r0b0t1cu/Tastatura-Cobra/IMG/IMG_9379.jpg

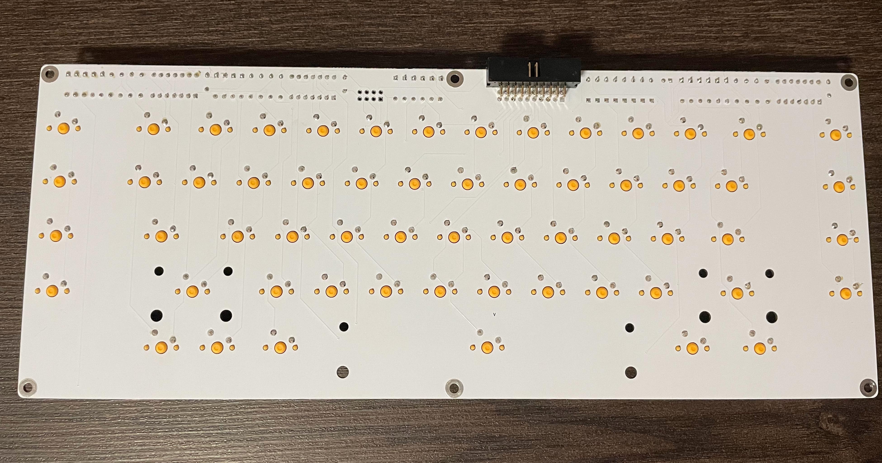
IMG/IMG_9379.jpg
