r0b0t1cu/Tastatura-Cobra/IMG/IMG_9391.jpg

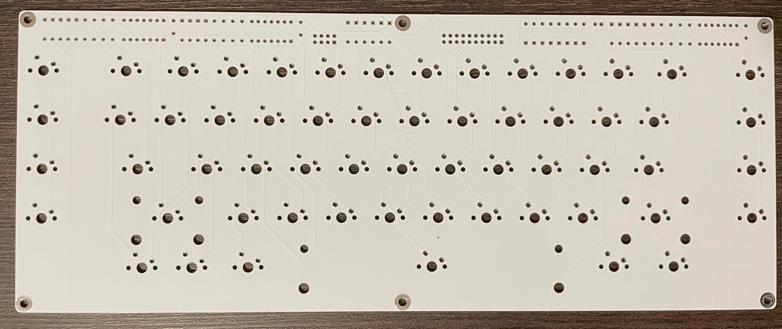
IMG/IMG_9391.jpg
